bluster980/Digital-Rain-Measurement-System/design_files/Alternate_Designs/Tipping_bucket_rain_gauge/image.png

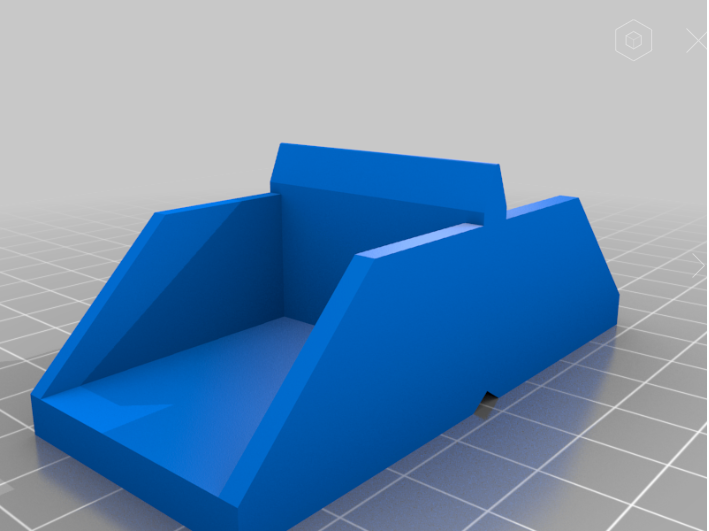
design_files/Alternate_Designs/Tipping_bucket_rain_gauge/image.png
