bluster980/Digital-Rain-Measurement-System/design_files/Alternate_Designs/Tipping_bucket_rain_gauge_01/images/Untitled.png

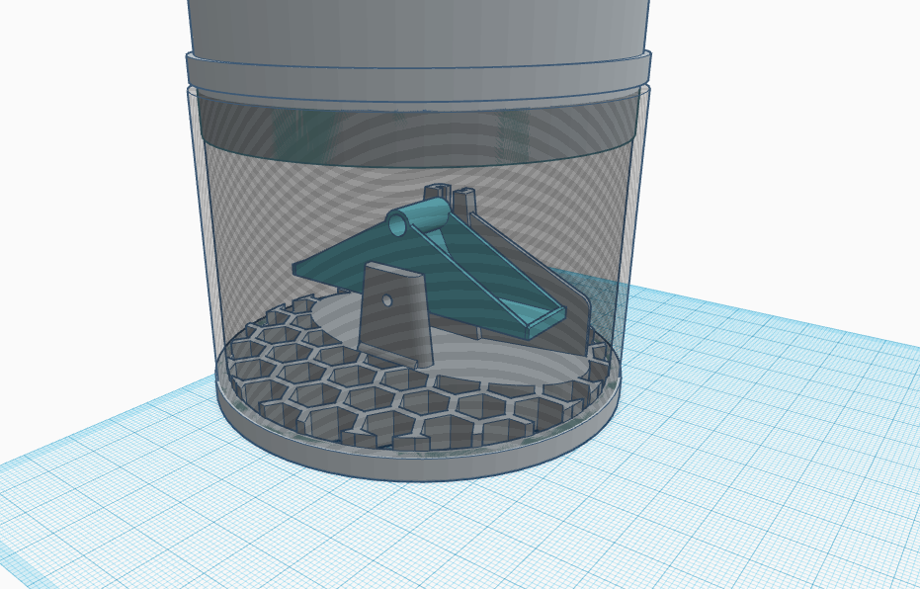
design_files/Alternate_Designs/Tipping_bucket_rain_gauge_01/images/Untitled.png
