bluster980/Digital-Rain-Measurement-System/design_files/Alternate_Designs/Tipping_Bucket_Rain_Gauge_for_HT_DN_110_pipe/images/IMG_20190714_002427_web.jpg

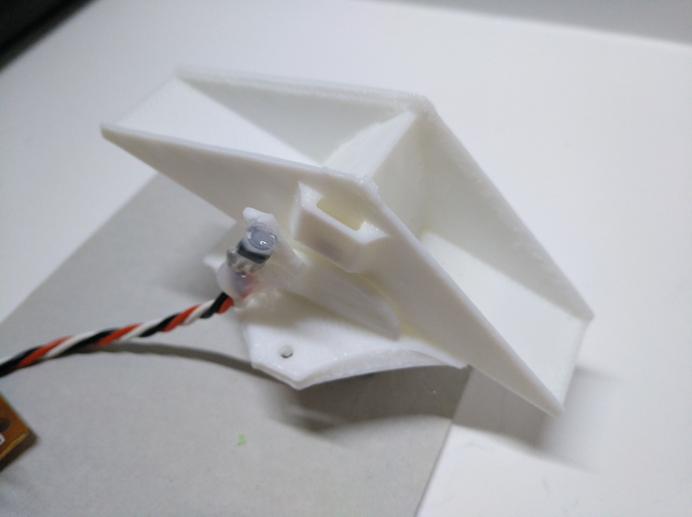
design_files/Alternate_Designs/Tipping_Bucket_Rain_Gauge_for_HT_DN_110_pipe/images/IMG_20190714_002427_web.jpg
